lgmarin/defuma_IoT/include/wifi_mgr.h

#ifndef wifi_mgr
#define wifi_mgr

#include <Arduino.h>

#define LED_ON      LOW
#define LED_OFF     HIGH

// From v1.1.1
// You only need to format the filesystem once
//#define FORMAT_FILESYSTEM       true
#define FORMAT_FILESYSTEM         false

#define MIN_AP_PASSWORD_SIZE    8

#define SSID_MAX_LEN            32
//From v1.0.10, WPA2 passwords can be up to 63 characters long.
#define PASS_MAX_LEN            64

#define NUM_WIFI_CREDENTIALS      1

// Assuming max 49 chars
#define TZNAME_MAX_LEN            50
#define TIMEZONE_MAX_LEN          50

// Use false if you don't like to display Available Pages in Information Page of Config Portal
// Comment out or use true to display Available Pages in Information Page of Config Portal
// Must be placed before #include <ESP_WiFiManager.h>
#define USE_AVAILABLE_PAGES     true

// From v1.0.10 to permit disable/enable StaticIP configuration in Config Portal from sketch. Valid only if DHCP is used.
// You'll loose the feature of dynamically changing from DHCP to static IP, or vice versa
// You have to explicitly specify false to disable the feature.
//#define USE_STATIC_IP_CONFIG_IN_CP          false
#define USE_DHCP_IP               true
#define USE_CONFIGURABLE_DNS      false

// Use false to disable NTP config. Advisable when using Cellphone, Tablet to access Config Portal.
// See Issue 23: On Android phone ConfigPortal is unresponsive (https://github.com/khoih-prog/ESP_WiFiManager/issues/23)
#define USE_ESP_WIFIMANAGER_NTP     false

// Just use enough to save memory. On ESP8266, can cause blank ConfigPortal screen
// if using too much memory
#define USING_AMERICA       true

// Use true to enable CloudFlare NTP service. System can hang if you don't have Internet access while accessing CloudFlare
// See Issue #21: CloudFlare link in the default portal (https://github.com/khoih-prog/ESP_WiFiManager/issues/21)
#define USE_CLOUDFLARE_NTP          false

// New in v1.0.11
#define USING_CORS_FEATURE          false

#define WIFICHECK_INTERVAL          1000L

// SSID and PW for your Router
// extern String Router_SSID;
// extern String Router_Pass;
//////

typedef struct
{
  char wifi_ssid[SSID_MAX_LEN];
  char wifi_pw  [PASS_MAX_LEN];
} WiFi_Credentials;

typedef struct
{
  WiFi_Credentials  WiFi_Creds [NUM_WIFI_CREDENTIALS];
  char TZ_Name[TZNAME_MAX_LEN];     // "America/Toronto"
  char TZ[TIMEZONE_MAX_LEN];        // "EST5EDT,M3.2.0,M11.1.0"
  uint16_t checksum;
} WM_Config;

typedef struct
{
  char temp_max[3];
  char temp_min[3];
} APP_Config;


extern WM_Config         WM_config;
extern APP_Config        APP_config;

#endif
